Beirdo/seeeduino-xiao-isp-programmer/hardware/xiao-isp-programmer/xiao-isp-programmer.kicad_sch

## KiCad design hardware/xiao-isp-programmer/xiao-isp-programmer.kicad_sch (2023-02-08)

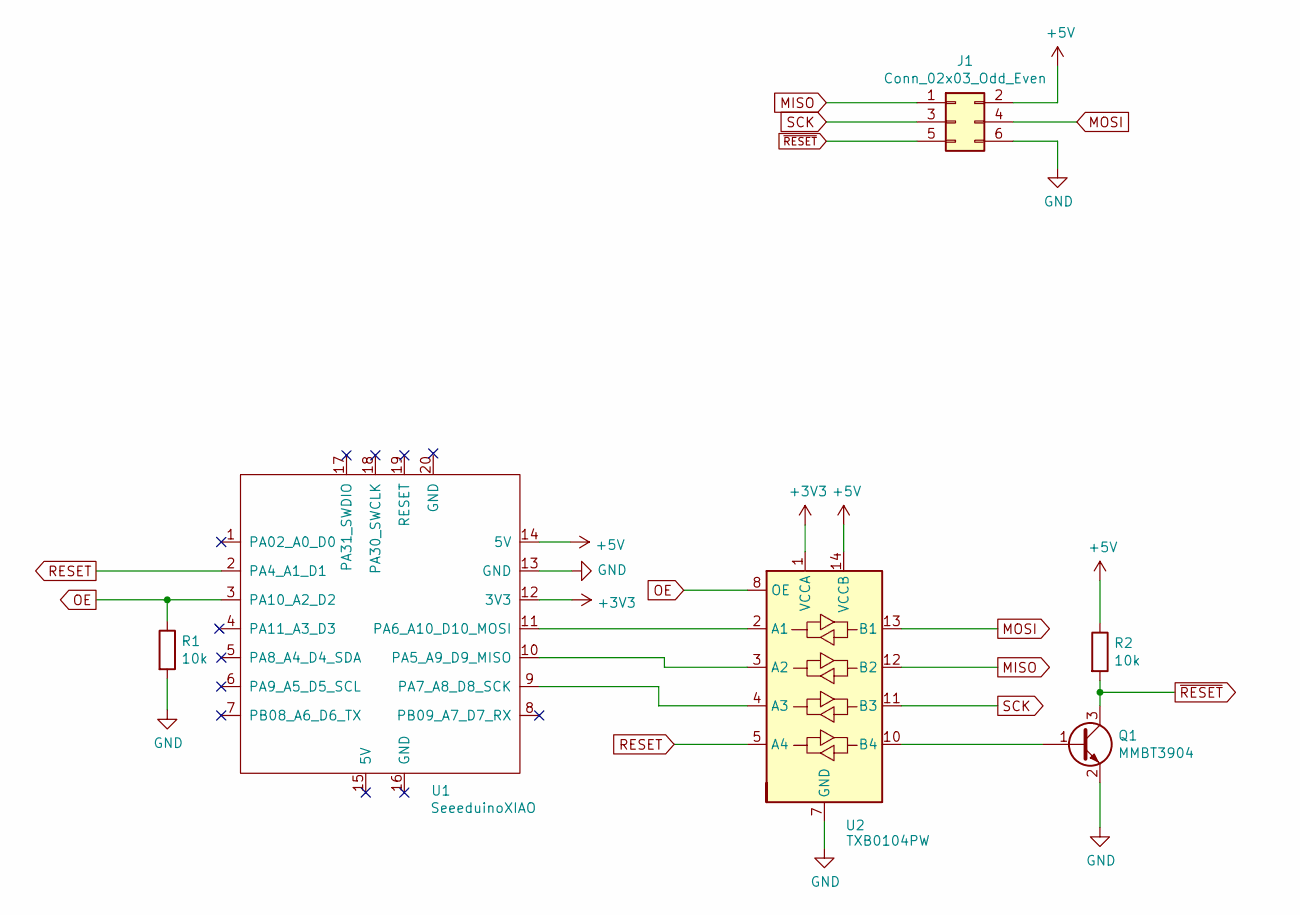
[picture p3: schematic xiao-isp-programmer.kicad_sch]

Parts:
J1: Conn_02x03_Odd_Even; PinHeader_2x03_P2.54mm_Vertical
Q1: MMBT3904; SOT-23
R1, R2: 10k; R_0805_2012Metric_Pad1.20x1.40mm_HandSolder
U1: SeeeduinoXIAO; Seeeduino XIAO-MOUDLE14P-2.54-21X17.8MM
U2: TXB0104PW; TSSOP-14_4.4x5mm_P0.65mm

Connections:
+3V3: U1.12 (3V3), U2.1 (VCCA)
+5V: J1.2, R2.1, U1.14 (5V), U2.14 (VCCB)
GND: J1.6, Q1.2 (E), R1.2, U1.13 (GND), U2.7 (GND)
MISO: J1.1, U2.12 (B2)
MOSI: J1.4, U2.13 (B1)
unnamed: Q1.1 (B), U2.10 (B4)
unnamed: U1.9 (PA7_A8_D8_SCK), U2.4 (A3)
unnamed: U1.10 (PA5_A9_D9_MISO), U2.3 (A2)
unnamed: U1.11 (PA6_A10_D10_MOSI), U2.2 (A1)
OE: R1.1, U1.3 (PA10_A2_D2), U2.8 (OE)
RESET: U1.2 (PA4_A1_D1), U2.5 (A4)
SCK: J1.3, U2.11 (B3)
~RESET: J1.5, Q1.3 (C), R2.2
